TKJElectronics/ATtinyRemote/PCB/Images for Gerber files/ATtinyRemote.boardoutline.ger.png

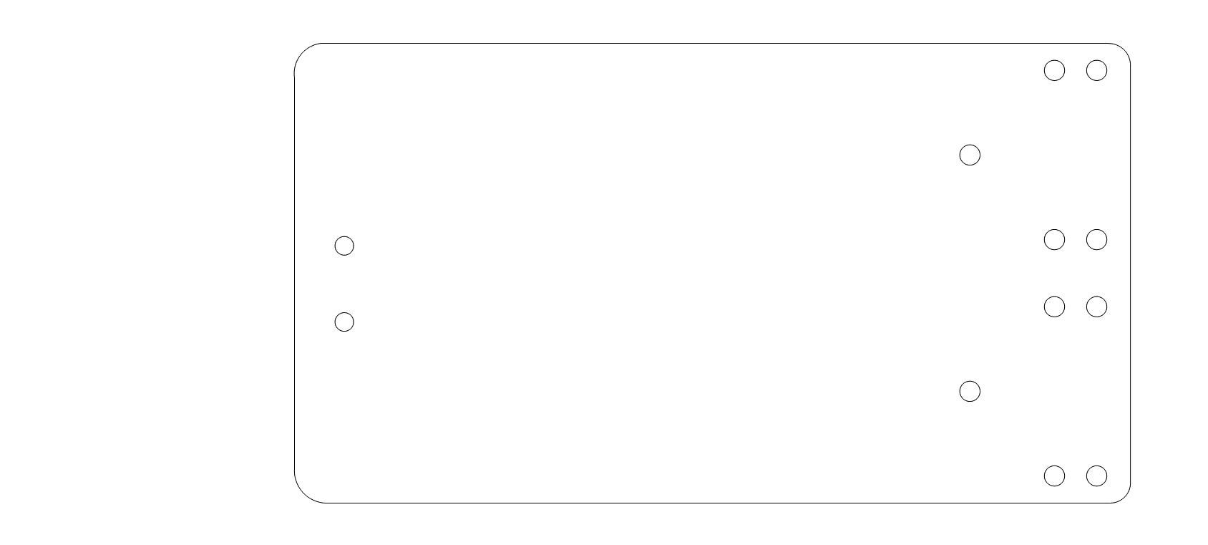
PCB/Images for Gerber files/ATtinyRemote.boardoutline.ger.png
